gugray/DotDotTilt/code/src/canvas.cpp

#include <Arduino.h>
#include <avr/pgmspace.h>
#include <font_6x8.h>
#include "canvas.h"

Canvas::Canvas()
{
	clear();
}

void Canvas::clear()
{
	dirty = true;
	uint16_t i = 0;
	for (uint8_t p = 0; p < N_ROWS / 8; ++p)
	{
		for (uint8_t x = 0; x < N_COLS; ++x, ++i)
		{
			pixels[i] = 0;
		}
	}
}

void Canvas::setPixel(uint8_t x, uint8_t y, bool on)
{
	dirty = true;
	uint16_t row = y / 8;
	uint8_t bit = y % 8;
	if (on)
		pixels[row * N_COLS + x] |= (1 << bit);
	else
		pixels[row * N_COLS + x] &= ~(1 << bit);
}

void Canvas::line(uint8_t x1, uint8_t y1, uint8_t x2, uint8_t y2)
{
  float dx = x2 - x1;
  float dy = y2 - y1;
  float len = round(sqrt(dx*dx + dy*dy));
  for (float i = 0; i <= len; i += 1)
	{
		float x = x1 + dx * i / len;
		float y = y1 + dy * i / len;
		setPixel(round(x), round(y), true);
	}
}

void Canvas::fwText(uint8_t x, uint8_t line, const char *str)
{
	dirty = true;
	const byte *fontData = font_6x8;
	uint8_t firstCode = pgm_read_byte(&fontData[2]); // get first defined character
	uint8_t lastCode = pgm_read_byte(&fontData[3]);	 // get last defined character
	uint8_t charWidth = 6;													 // width in pixel of one char

	uint16_t arrPos = line * N_COLS + x;
	for (; *str != 0; ++str)
	{
		uint8_t charVal = *str;
		if (charVal < firstCode || charVal > lastCode)
			continue;

		uint16_t fontDataPos = 8 + (uint16_t)(charVal - firstCode) * charWidth;

		uint8_t nCols = charWidth;
		if (x + charWidth > N_COLS) // stay inside display area
			nCols = N_COLS - x;

		for (uint8_t i = 0; i < nCols; i++, arrPos++)
		{
			pixels[arrPos] = pgm_read_byte(&fontData[fontDataPos + i]);
		}
	}
}
